e3w2q/te96-keyboard/doc/custom_layout/image/ortholinear.png

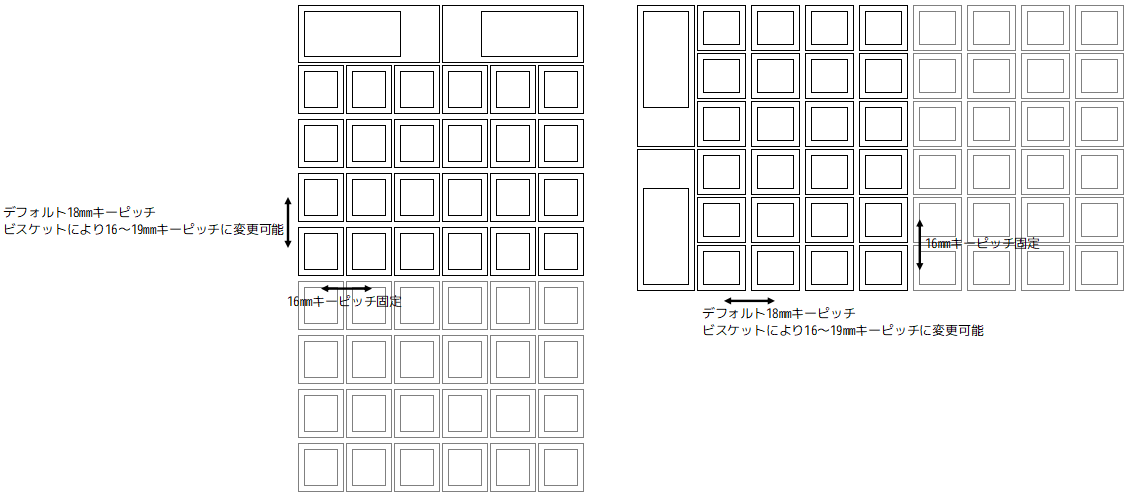
doc/custom_layout/image/ortholinear.png
