e3w2q/te96-keyboard/doc/natto48/image/pinheader_attach.jpg

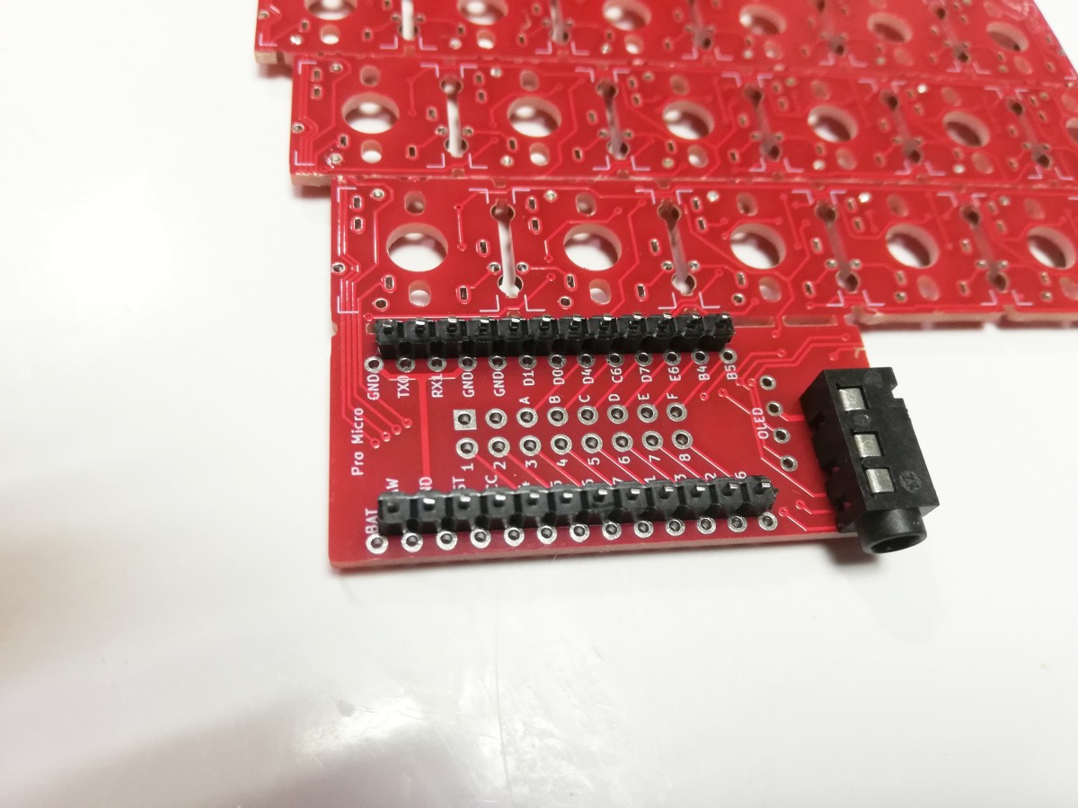
doc/natto48/image/pinheader_attach.jpg
