e3w2q/te96-keyboard/pcb/te96.sch

## KiCad design pcb/te96.sch (2020-08-19)

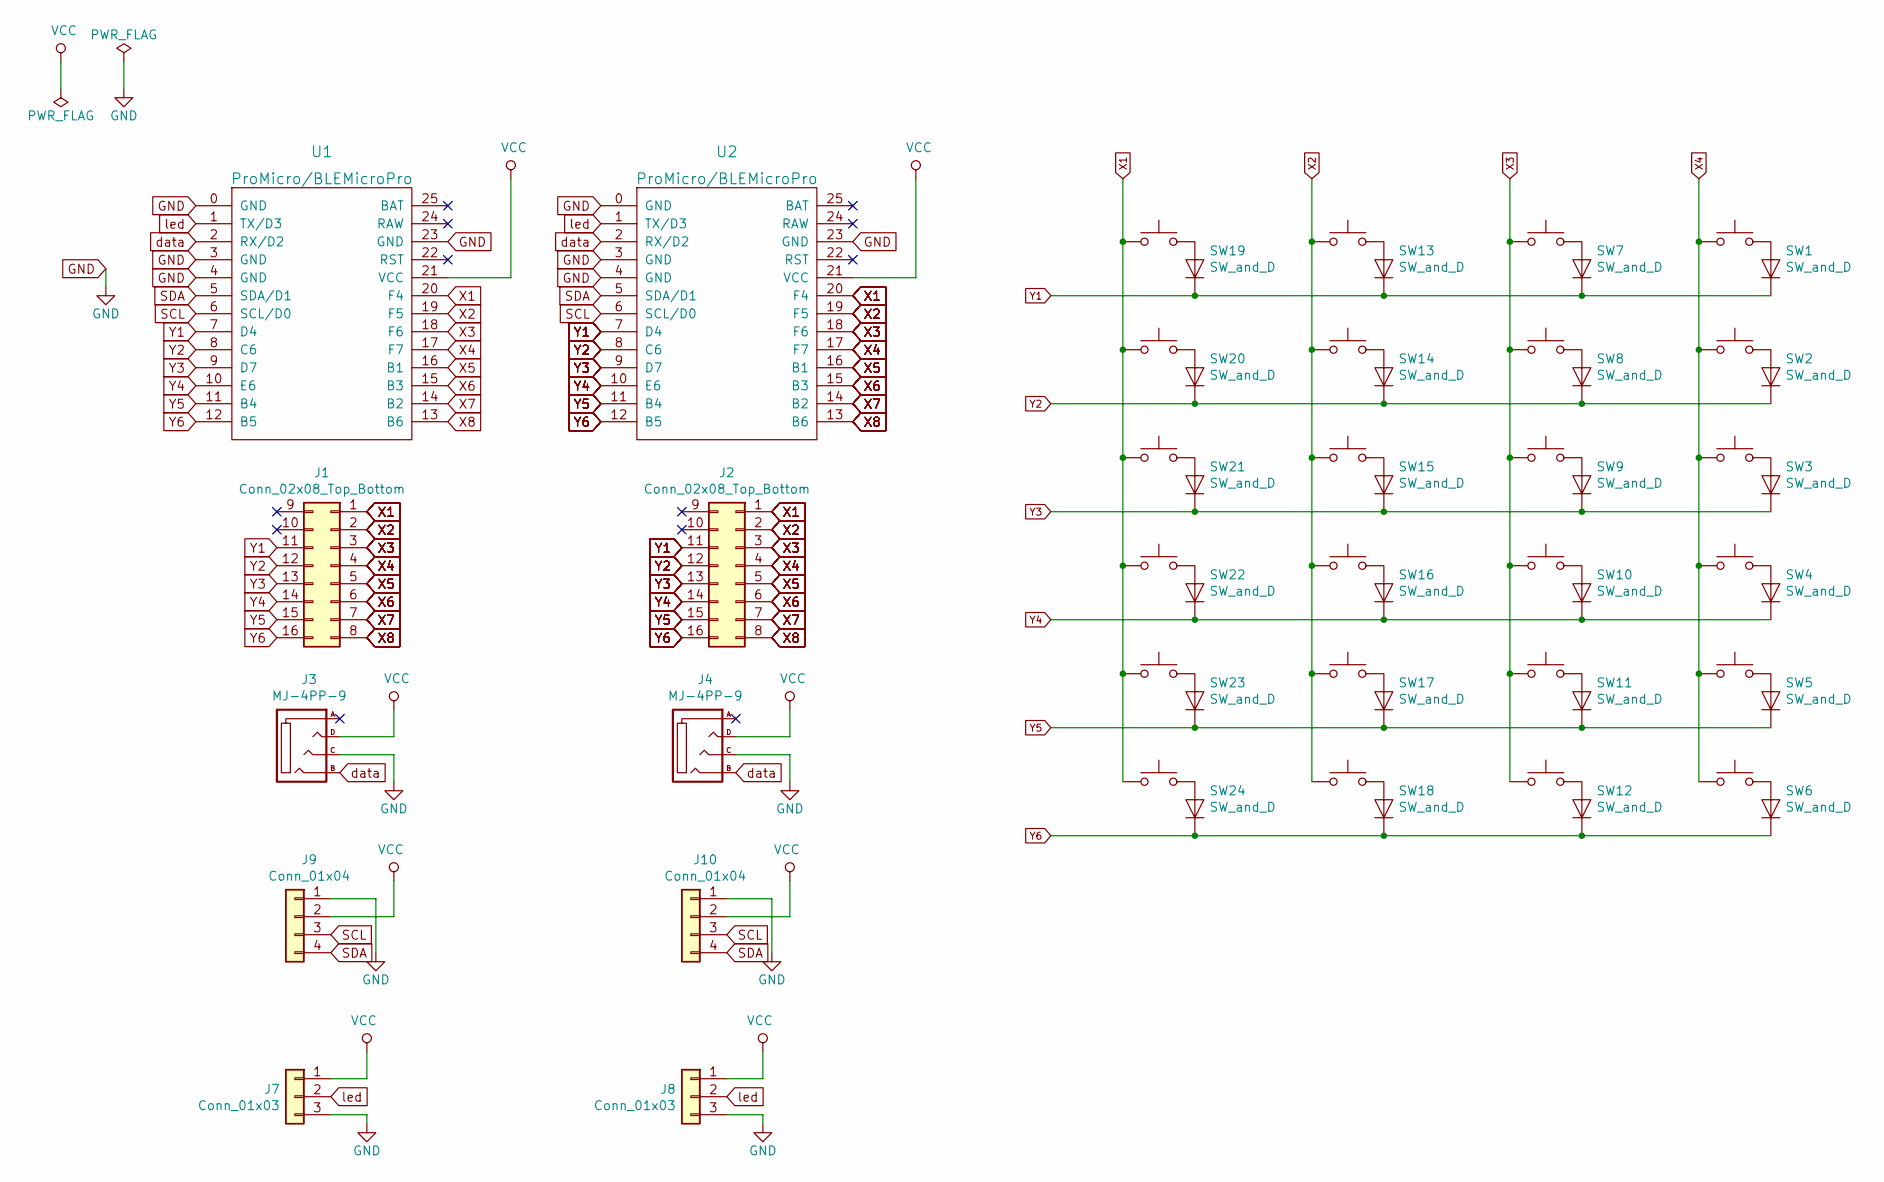
[picture p68: schematic te96.sch]

Parts:
J1, J2: Conn_02x08_Top_Bottom; IDC-Header_2x08_P2.54mm_rev2
J3, J4: MJ-4PP-9
J7, J8: Conn_01x03; StripLED_rev2
J9, J10: Conn_01x04; OLED_rev2
SW1, SW2, SW3, SW4, SW5, SW6, SW7, SW8, SW9, SW10, SW11, SW12, SW13, SW14, SW15, SW16, SW17, SW18, SW19, SW20, SW21, SW22, SW23, SW24: SW_and_D; CherryMX_MidHeight_Choc_16mm_rev8
U1, U2: ProMicro/BLEMicroPro; ArduinoProMicro-ZigZag-BLEMicroPro-Multi-rev2

Connections:
GND: J3.C, J4.C, J7.3, J8.3, J9.1, J10.1, U1.0 (GND), U1.3 (GND), U1.4 (GND), U1.23 (GND), U2.0 (GND), U2.3 (GND), U2.4 (GND), U2.23 (GND)
SCL: J9.3, J10.3, U1.6 (SCL/D0), U2.6 (SCL/D0)
SDA: J9.4, J10.4, U1.5 (SDA/D1), U2.5 (SDA/D1)
VCC: J3.D, J4.D, J7.1, J8.1, J9.2, J10.2, U1.21 (VCC), U2.21 (VCC)
X1: J1.1, J2.1, SW19.1, SW20.1, SW21.1, SW22.1, SW23.1, SW24.1, U1.20 (F4), U2.20 (F4)
X2: J1.2, J2.2, SW13.1, SW14.1, SW15.1, SW16.1, SW17.1, SW18.1, U1.19 (F5), U2.19 (F5)
X3: J1.3, J2.3, SW7.1, SW8.1, SW9.1, SW10.1, SW11.1, SW12.1, U1.18 (F6), U2.18 (F6)
X4: J1.4, J2.4, SW1.1, SW2.1, SW3.1, SW4.1, SW5.1, SW6.1, U1.17 (F7), U2.17 (F7)
X5: J1.5, J2.5, U1.16 (B1), U2.16 (B1)
X6: J1.6, J2.6, U1.15 (B3), U2.15 (B3)
X7: J1.7, J2.7, U1.14 (B2), U2.14 (B2)
X8: J1.8, J2.8, U1.13 (B6), U2.13 (B6)
Y1: J1.11, J2.11, SW1.2, SW7.2, SW13.2, SW19.2, U1.7 (D4), U2.7 (D4)
Y2: J1.12, J2.12, SW2.2, SW8.2, SW14.2, SW20.2, U1.8 (C6), U2.8 (C6)
Y3: J1.13, J2.13, SW3.2, SW9.2, SW15.2, SW21.2, U1.9 (D7), U2.9 (D7)
Y4: J1.14, J2.14, SW4.2, SW10.2, SW16.2, SW22.2, U1.10 (E6), U2.10 (E6)
Y5: J1.15, J2.15, SW5.2, SW11.2, SW17.2, SW23.2, U1.11 (B4), U2.11 (B4)
Y6: J1.16, J2.16, SW6.2, SW12.2, SW18.2, SW24.2, U1.12 (B5), U2.12 (B5)
data: J3.B, J4.B, U1.2 (RX/D2), U2.2 (RX/D2)
led: J7.2, J8.2, U1.1 (TX/D3), U2.1 (TX/D3)
